MOSH-Insa-Toulouse/2022-2023-4GP-FRONZES-CHAKRI/LTSpice/capteur.asc

B1: bi; I=V(cp,cn)*({G0}+V(gc,gn)*{G1})
C1: cap; 0.2m
R1: res; {R1}
Named nets: cn, cp, gp, gn, gc
