MOSH-Insa-Toulouse/2022-2023-4GP-FRONZES-CHAKRI/LTSpice/circuit.asc

5V: voltage; 5
C1: cap; 100n
C2: cap; 100n
C4: cap; 0.01m
C5: cap; 1p
R1: res; 100k
R2: res; 1k
R3: res; 100k
R5: res; 10k
R6: res; 1k
U1: LTC1050
V1: voltage; PULSE(0 1 0.2 0.1 0.1 10)
V2: voltage; SINE(0 325 50)
X1: graphite
Named nets: 0, 5V, Isens, ADC
.tran 12
;ac oct 200 0.1 100
.param G0 10n
.param G1 10n
.param R1 1k
